zhol0777/bully-files/pcb/marbastlib/3d/ROT_EC11E.step

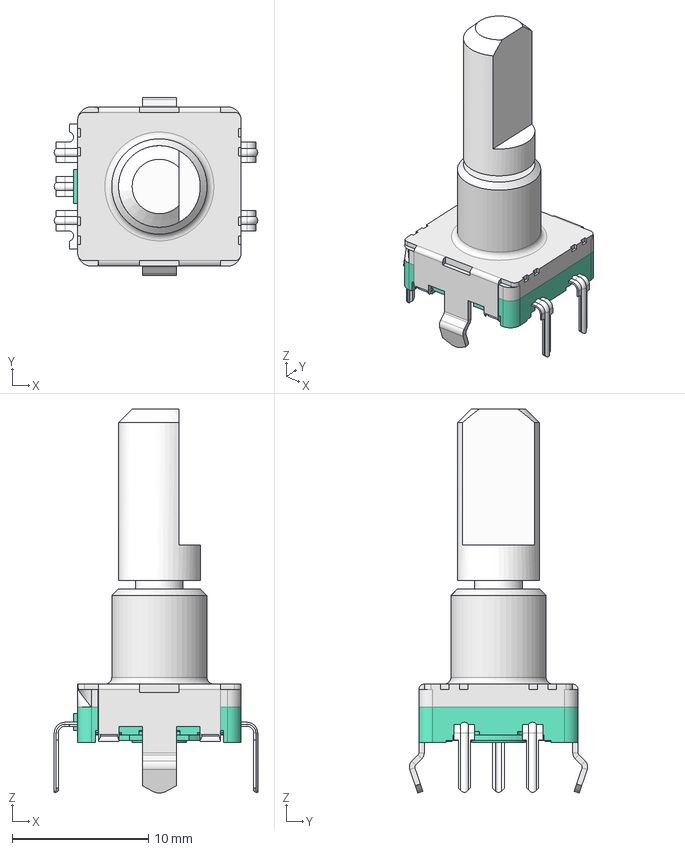
[picture p15: CAD file, 2023-12-29]
pcb/marbastlib/3d/ROT_EC11E.step
14.9 x 13.1 x 28.2 mm
