zhol0777/bully-files/pcb/marbastlib/3d/SW_SSSS213100.step

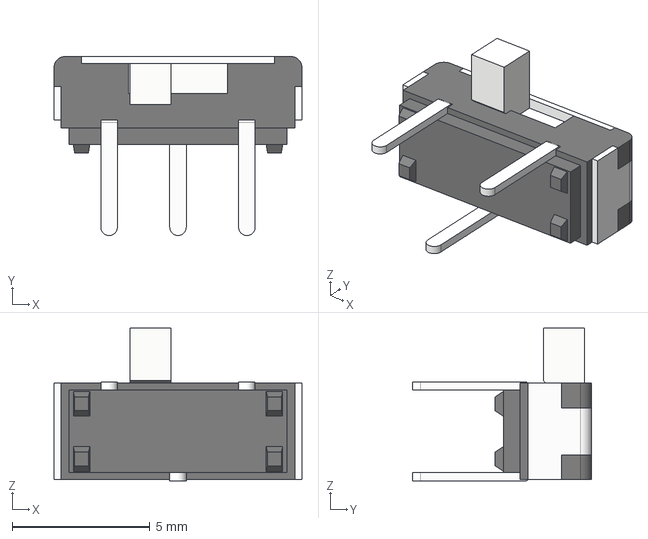
[picture p16: CAD file, 2023-12-29]
pcb/marbastlib/3d/SW_SSSS213100.step
9.00 x 6.50 x 5.55 mm
