zhol0777/bully-files/pcb/marbastlib/3d/ROT_EC11N.step

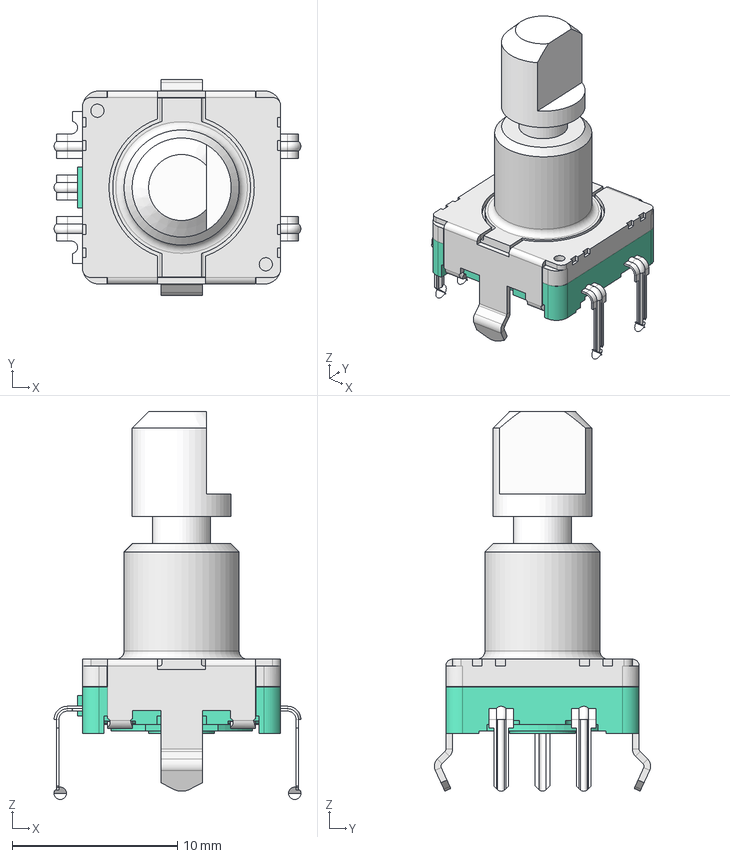
[picture p17: CAD file, 2023-12-29]
pcb/marbastlib/3d/ROT_EC11N.step
14.9 x 13.1 x 23.5 mm
