zhol0777/bully-files/pcb/marbastlib/3d/CON_TYPE-C-31-M-12.step

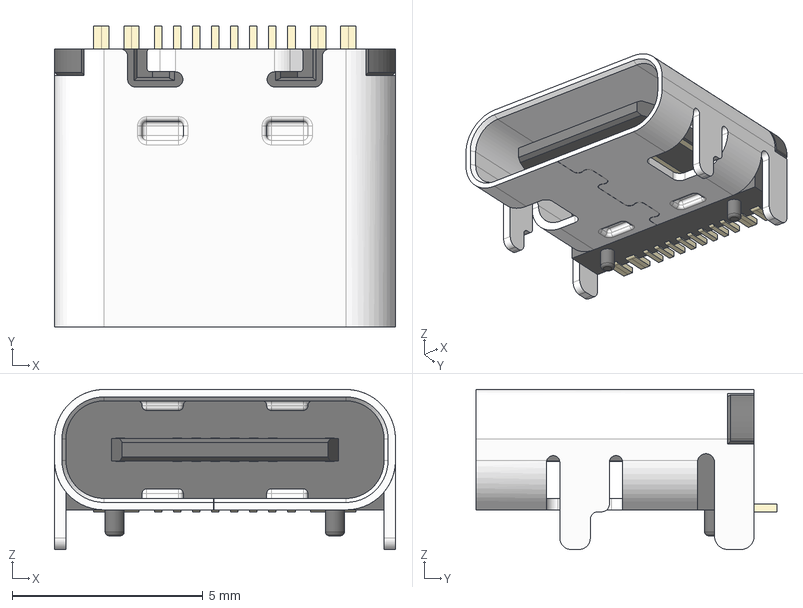
[picture p18: CAD file, 2023-12-29]
pcb/marbastlib/3d/CON_TYPE-C-31-M-12.step
8.95 x 7.90 x 4.20 mm
ConPins
PcbPins
Mold
Frame
