zhol0777/bully-files/pcb/marbastlib/3d/HS_Kailh_MX.step

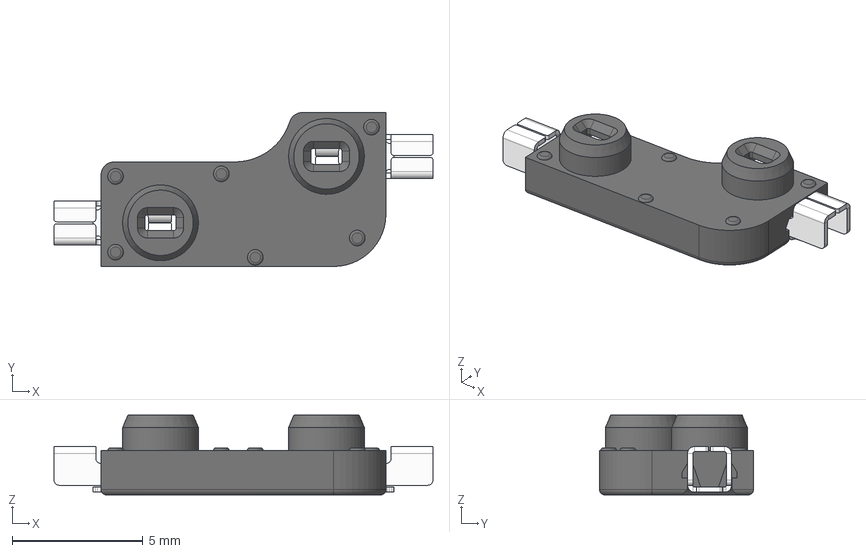
[picture p19: CAD file, 2023-12-29]
pcb/marbastlib/3d/HS_Kailh_MX.step
14.5 x 5.89 x 3.05 mm
Contact x 2
