zhol0777/bully-files/pcb/marbastlib/3d/CON_SM13B-SRSS-TB.step

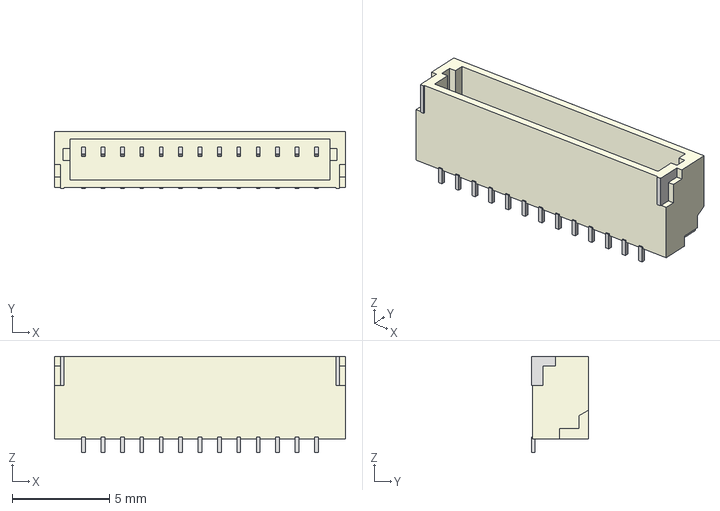
[picture p20: CAD file, 2023-12-29]
pcb/marbastlib/3d/CON_SM13B-SRSS-TB.step
15.0 x 2.96 x 4.95 mm
