zhol0777/bully-files/pcb/marbastlib/3d/moko_mk08a_nRF52840.step

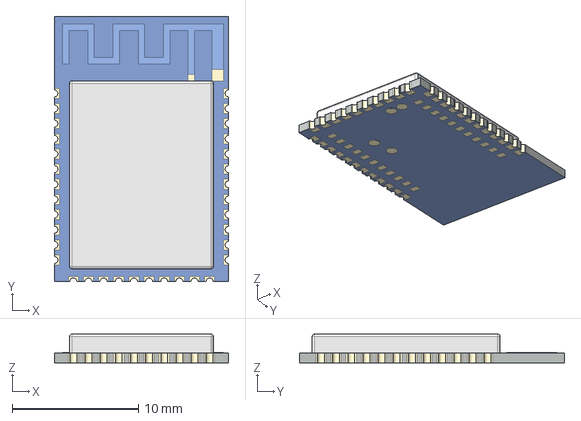
[picture p21: CAD file, 2023-12-29]
pcb/marbastlib/3d/moko_mk08a_nRF52840.step
13.8 x 21.0 x 2.29 mm
