zhol0777/bully-files/pcb/marbastlib/3d/PNT_RKJXU1210006.step

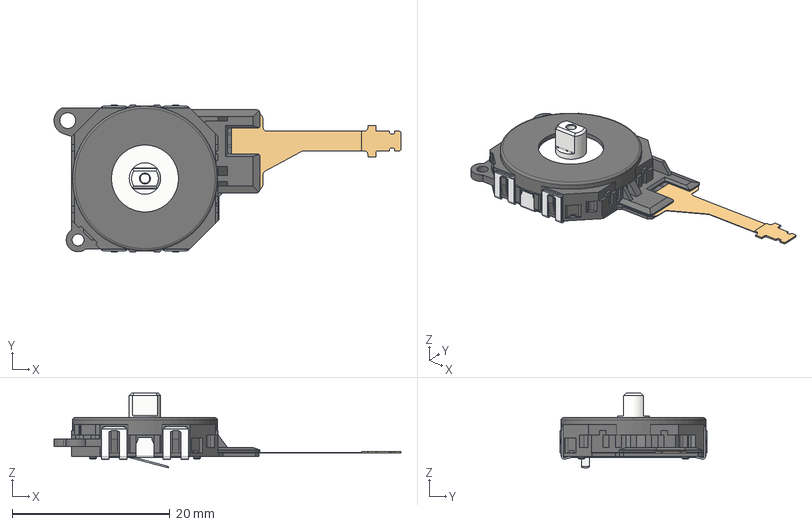
[picture p22: CAD file, 2023-12-29]
pcb/marbastlib/3d/PNT_RKJXU1210006.step
44.0 x 18.6 x 9.50 mm
