zhol0777/bully-files/pcb/marbastlib/3d/CON_SM04B-SRSS-TB.step

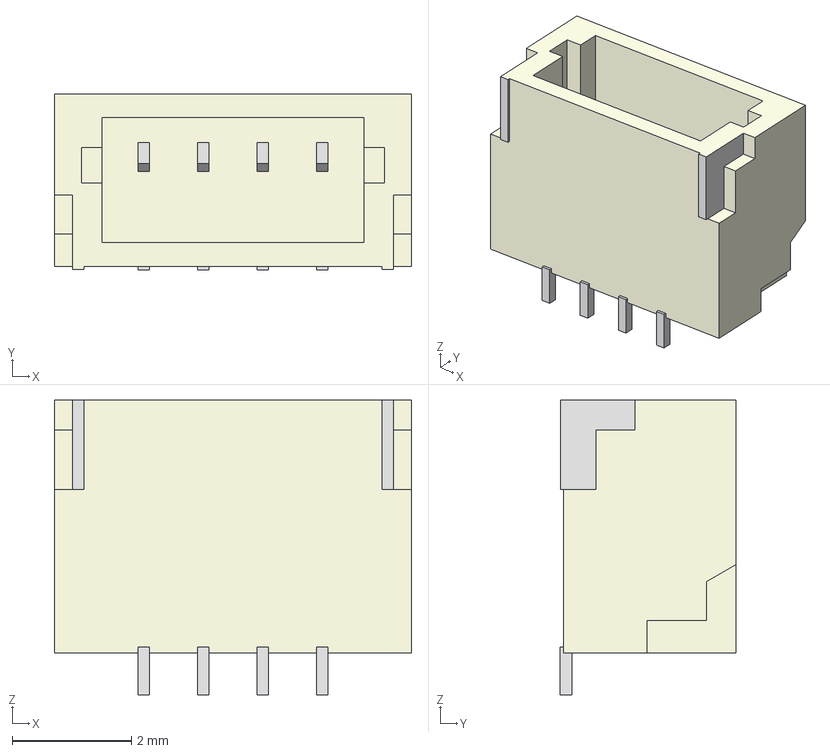
[picture p23: CAD file, 2023-12-29]
pcb/marbastlib/3d/CON_SM04B-SRSS-TB.step
6.00 x 2.96 x 4.95 mm
