zhol0777/bully-files/pcb/marbastlib/3d/CON_TYPE-C-31-M-14.step

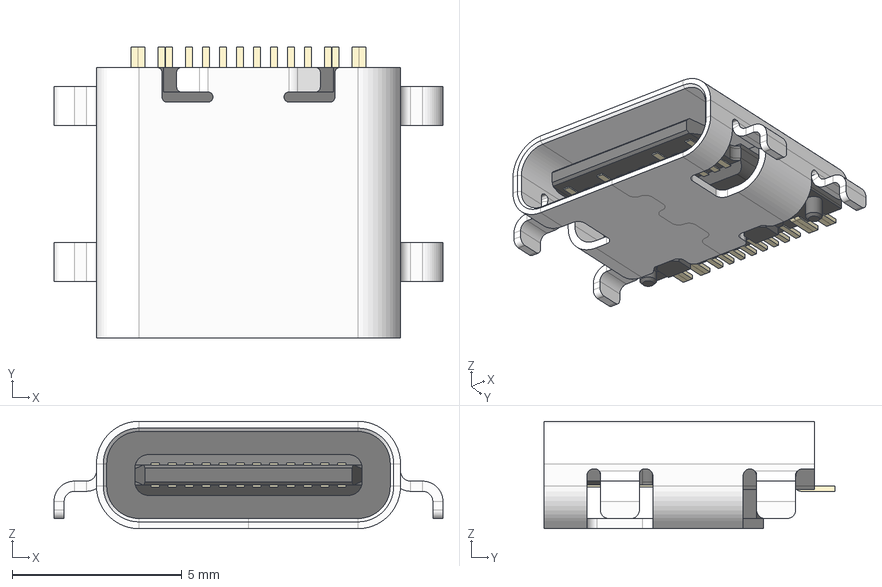
[picture p24: CAD file, 2023-12-29]
pcb/marbastlib/3d/CON_TYPE-C-31-M-14.step
11.5 x 8.56 x 3.16 mm
Shroud
Plastic Body & Connector
