zhol0777/bully-files/pcb/marbastlib/3d/HS_Kailh_Choc.step

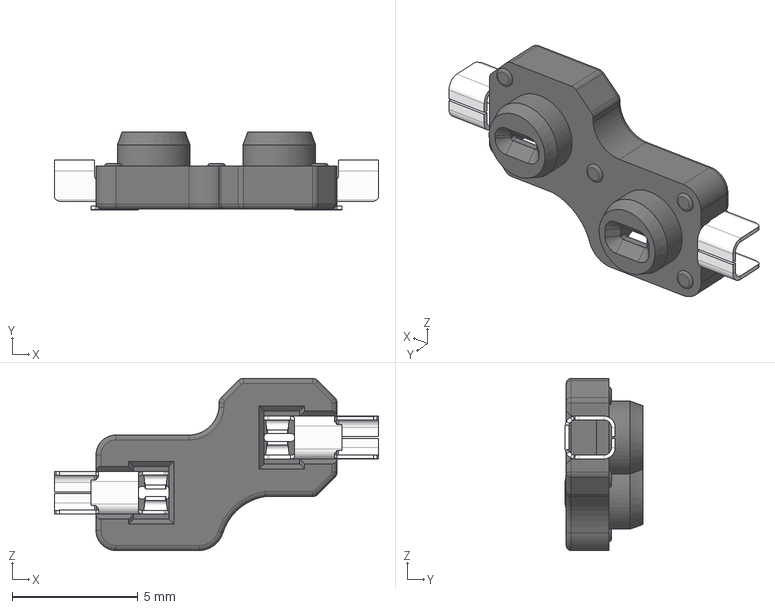
[picture p25: CAD file, 2023-12-29]
pcb/marbastlib/3d/HS_Kailh_Choc.step
12.9 x 3.09 x 6.85 mm
pin x 2
socket
