zhol0777/bully-files/pcb/marbastlib/3d/CON_BM02B-ACHSS.step

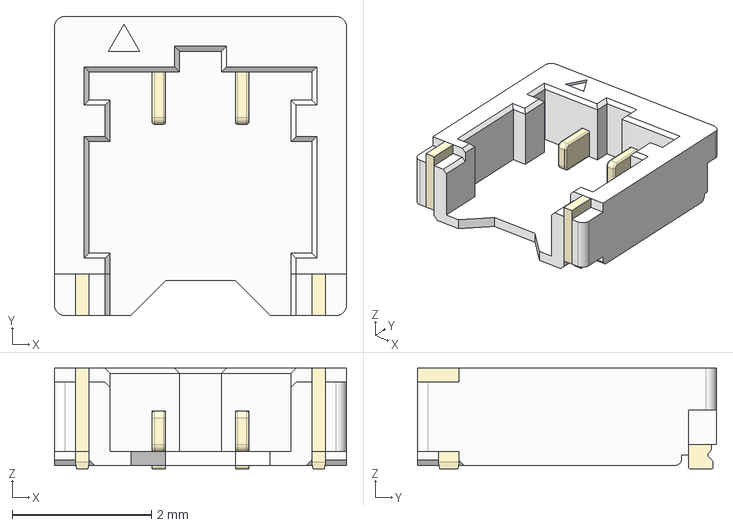
[picture p26: CAD file, 2023-12-29]
pcb/marbastlib/3d/CON_BM02B-ACHSS.step
4.20 x 4.30 x 1.45 mm
