zhol0777/bully-files/pcb/marbastlib/3d/SW_ESP3020.step

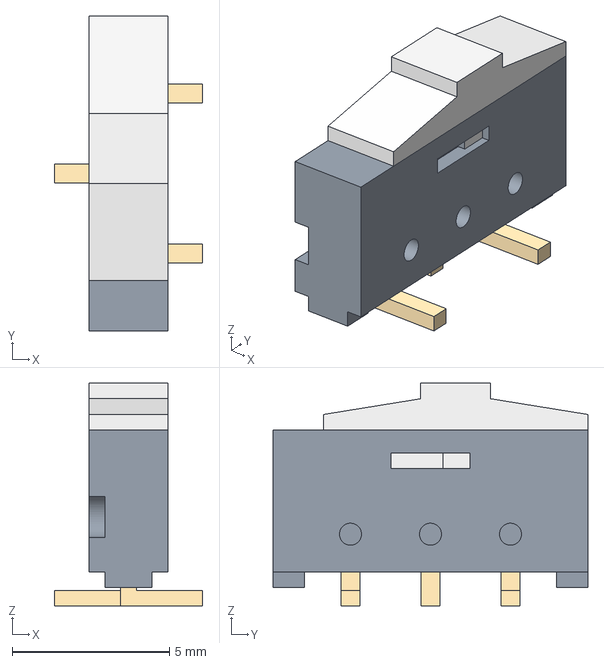
[picture p28: CAD file, 2023-12-29]
pcb/marbastlib/3d/SW_ESP3020.step
4.70 x 10.0 x 7.08 mm
