zhol0777/bully-files/pcb/marbastlib/3d/CON_SM06B-SRSS-TB.step

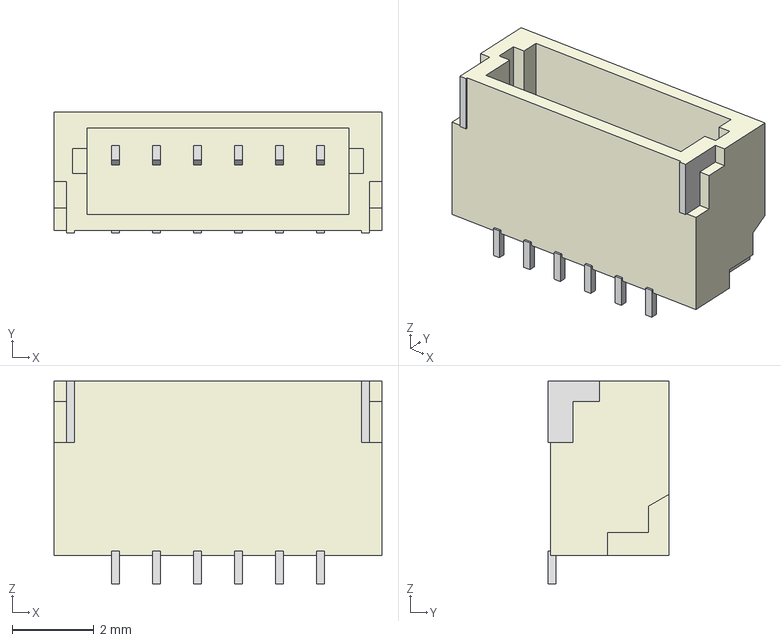
[picture p29: CAD file, 2023-12-29]
pcb/marbastlib/3d/CON_SM06B-SRSS-TB.step
8.00 x 2.96 x 4.95 mm
