zhol0777/bully-files/pcb/marbastlib/3d/PNT_psp1000.step

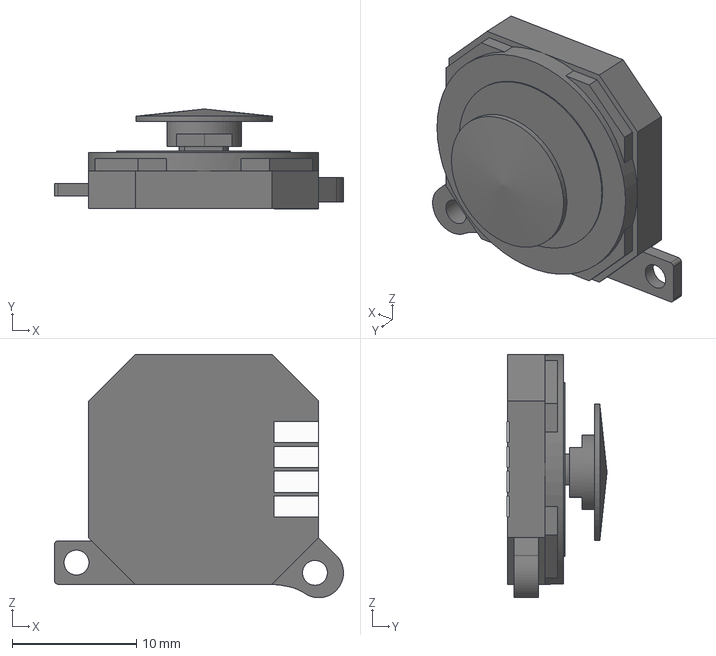
[picture p30: CAD file, 2023-12-29]
pcb/marbastlib/3d/PNT_psp1000.step
23.2 x 8.05 x 19.6 mm
