zhol0777/bully-files/pcb/marbastlib/3d/CON_MJ-4PP-9.step

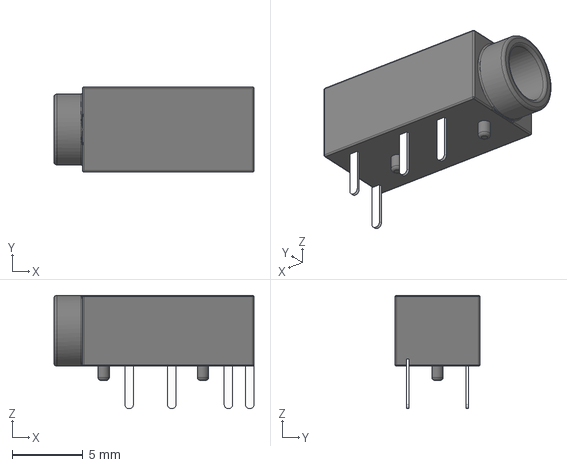
[picture p31: CAD file, 2023-12-29]
pcb/marbastlib/3d/CON_MJ-4PP-9.step
14.1 x 6.00 x 8.00 mm
