zhol0777/bully-files/pcb/marbastlib/3d/SW_SSSS223900.step

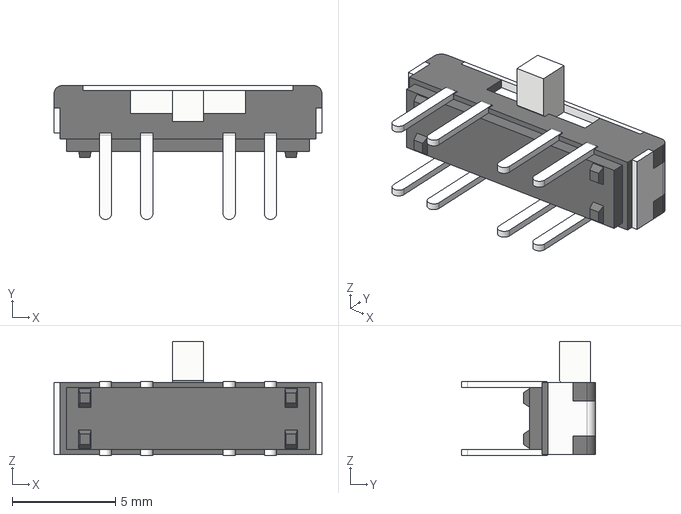
[picture p33: CAD file, 2023-12-29]
pcb/marbastlib/3d/SW_SSSS223900.step
13.0 x 6.50 x 5.55 mm
