zhol0777/bully-files/pcb/marbastlib/3d/LED_WS2812_2020.step

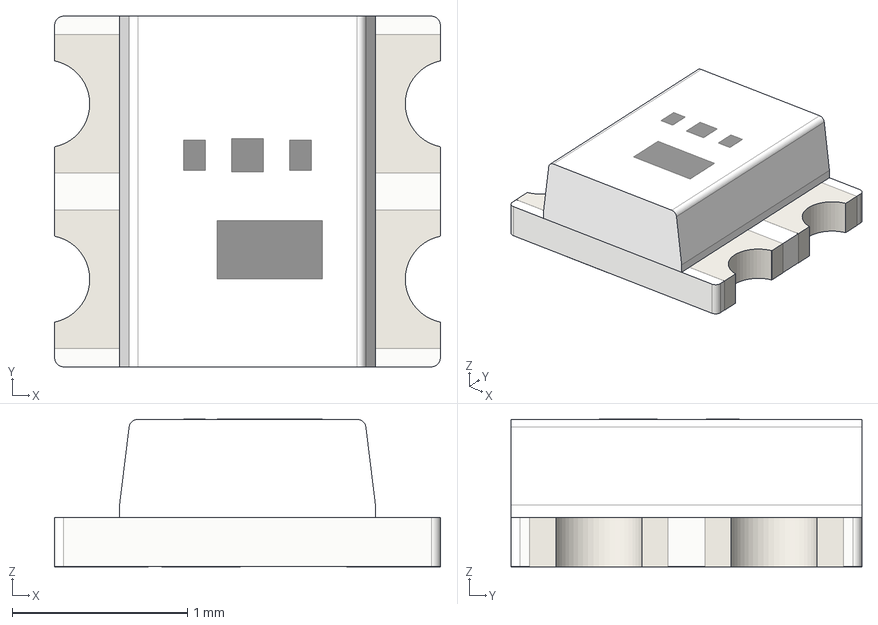
[picture p34: CAD file, 2023-12-29]
pcb/marbastlib/3d/LED_WS2812_2020.step
2.20 x 2.00 x 0.842 mm
